nesos-dev/nes-dev-cart/hardware/production/nes-dev-cart-render-bottom-3d.png

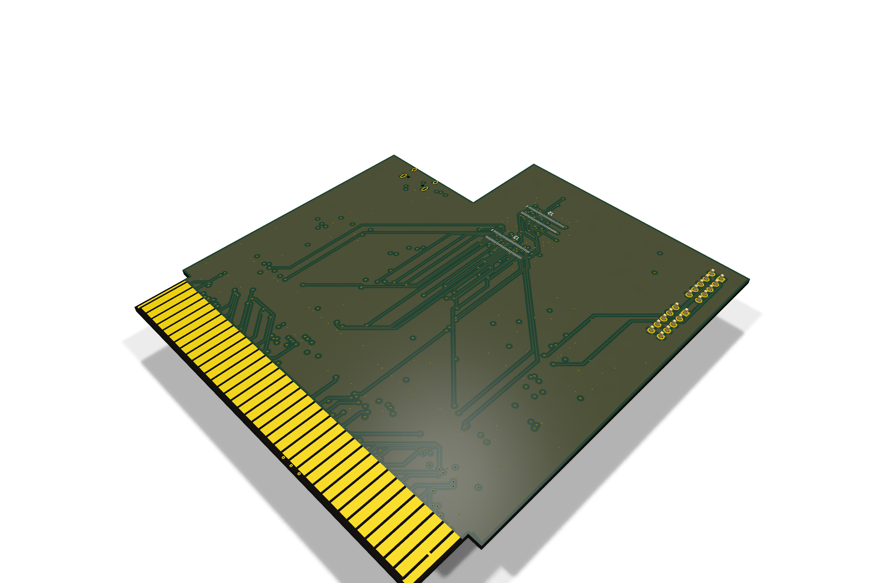
hardware/production/nes-dev-cart-render-bottom-3d.png
